Logan-M-51/Logan-M-51-NAVSEA-TestSet-PCB-Redesign/LtSpice-Test-Models/WheatstoneBridgeAlternative.asc

DET: res; 1
R3: res; 250
R5: res; 10k
R6: res; 10k
R8: res; 10k
R9: res; 10k
R11: res; 0.5
R13: res; 1.75
R14: res; 0.7
R15: res; 10k
R16: res; 10k
R17: res; 0.5
R18: res; 1.75
R19: res; 0.7
R20: res; 0
R21: res; 6
U1: OP191
U2: OP191
V1: voltage; 12
Named nets: 12vdc, 0, D, B, D2, B2
.model 2N2905A PNP(Is=650.6E-18 Xti=3 Eg=1.11 Vaf=115.7 Bf=231.7 Ne=1.829 Ise=54.81f Ikf=1.079 Xtb=1.5 Br=3.563 Nc=2 Isc=0 Ikr=0 Rc=.715 Cjc=14.76p Mjc=.5383 Vjc=.75 Fc=.5 Cje=19.82p Mje=.3357 Vje=.75 Tr=111.3n Tf=603.7p Itf=.65 Vtf=5 Xtf=1.7 Rb=10 Vceo=60 Icrating=600m mfg=Philips)
.model 2N2219 NPN(Is=14.34f Xti=3 Eg=1.11 Vaf=74.03 Bf=255.9 Ne=1.307 Ise=14.34f Ikf=.2847 Xtb=1.5 Br=6.092 Nc=2 Isc=0 Ikr=0 Rc=1 Cjc=7.306p Mjc=.3416 Vjc=.75 Fc=.5 Cje=22.01p Mje=.377 Vje=.75 Tr=46.91n Tf=411.1p Itf=.6 Vtf=1.7 Xtf=3 Rb=10 Vceo=30 Icrating=800m mfg=Philips)
.model 1N4004 D(Is=500p Rs=0.12 N=1.6 Tt=4u Cjo=40p M=0.35 BV=400 Ibv=5.00u Mfg=BobCordellBook Type=Silicon)
.model 1N746 D(Is=31.47f Rs=9.494 Ikf=0 N=1 Xti=3 Eg=1.11 Cjo=220p M=.5959 Vj=.75 Fc=.5 Isr=2.035n Nr=2 Bv=3.3 Ibv=45.862m Nbv=3.0477 Ibvl=29.831m Nbvl=11.606 Tbv1=-636.4u Vpk=3.3 mfg=Motorola type=zener)
.model 1N758 D(Is=1.953f Rs=2.305 Ikf=0 N=1 Xti=3 Eg=1.11 Cjo=68p M=.3856 Vj=.75 Fc=.5 Isr=1.939n Nr=2 Bv=10 Ibv=.16597 Nbv=.84122 Ibvl=1.003m Nbvl=.20892 Tbv1=650u)
.tran 0 5 0 0.1
A
C
B
D
LOW
HIGH
D
B
C
High
Low
readout
readout
set
set
