Logan-M-51/Logan-M-51-NAVSEA-TestSet-PCB-Redesign/LtSpice-Test-Models/working_model.asc

C1: cap; 0.1µ
C2: cap; 0.1µ
C3: cap; 0.047µ
C4: cap; 2.2µ
C5: cap; 2.2µ
C6: cap; 4.7µ
C7: cap; 4.7µ
C8: cap; 4.7µ
D1: LED
D2: diode; 1N4004
D3: diode; 1N4004
D4: diode; 1N4004
D5: diode; 1N4004
D6: zener; 1N746
D7: diode; 1N4004
D8: diode; 1N4004
D9: diode; 1N4004
D10: diode; 1N4004
Q1: npn; 2N2222
Q2: pnp; 2N2905A
Q3: pnp; 2N2905A
Q4: npn; 2N2219
Q5: npn; 2N2219
Q6: npn; 2N2219
Q7: npn; 2N2219
Q8: npn; 2N2219
Q9: pnp; 2N2905A
Q10: npn; 2N2219
Q11: npn; 2N2219
Q12: npn; 2N2219
Q13: npn; 2N2219
Q14: pnp; 2N2905A
R1: res; 10k
R2: res; 30k
R3: res; 22k
R4: res; 1k
R5: res; 22k
R6: res; 1800
R7: res; 1800
R8: res; 1.2k
R9: res; 680
R10: res; 68
R11: res; 82
R12: res; 470
R13: res; 0.91
R14: res; 10k
R15: res; 68.1k
R16: res; 178
R17: res; 1470
R18: res; 10k
R19: res; 178
R20: res; 1330
R21: res; 68.1k
R22: res; 330k
R23: res; 2200
R24: res; 10k
R25: res; 2200
R26: res; 10k
R27: res; 6800
R28: res; 110
R29: res; 1
R30: res; 147
R31: res; 99
R32: res; 1k
R33: res; 2200
R34: res; 10k
R35: res; 2200
R36: res; 10k
R37: res; 6800
R38: res; 287
R39: res; 31.6
R40: res; 74
R41: res; 26
V1: voltage; 5
V2: voltage; 12
Named nets: 0
.tran 0 500m 0 10u
.model 1N4004 D(Is=500p Rs=0.12 N=1.6 Tt=4u Cjo=40p M=0.35 BV=400 Ibv=5.00u Mfg=BobCordellBook Type=Silicon)
.model 1N746 D(Is=31.47f Rs=9.494 Ikf=0 N=1 Xti=3 Eg=1.11 Cjo=220p M=.5959 Vj=.75 Fc=.5 Isr=2.035n Nr=2 Bv=3.3 Ibv=45.862m Nbv=3.0477 Ibvl=29.831m Nbvl=11.606 Tbv1=-636.4u Vpk=3.3 mfg=Motorola type=zener)
.model 2N2905 PNP(IS=1E-14 VAF=120
+   BF=250 IKF=0.3 XTB=1.5 BR=3
+   CJC=8E-12 CJE=30E-12 TR=40E-9 TF=30E-9
+   ITF=1 VTF=2 XTF=3 RB=10 RC=.3 RE=.2 Vceo=60 Icrating=600m mfg=Philips)
.model 2N2219 NPN(Is=14.34f Xti=3 Eg=1.11 Vaf=74.03 Bf=255.9 Ne=1.307 Ise=14.34f Ikf=.2847 Xtb=1.5 Br=6.092 Nc=2 Isc=0 Ikr=0 Rc=1 Cjc=7.306p Mjc=.3416 Vjc=.75 Fc=.5 Cje=22.01p Mje=.377 Vje=.75 Tr=46.91n Tf=411.1p Itf=.6 Vtf=1.7 Xtf=3 Rb=10 Vceo=30 Icrating=800m mfg=Philips)
